diy-dream/shower-water-reusable/workspace/stm32-shower-water-reusable-stm32l412kb/Core/Src/stripEffects.c

/*
 * stripEffects.c
 *
 *  Created on: Aug 22, 2020
 *      Author: Alan
 */

#include "stripEffects.h"
#include "WS2812.h"

extern void setLEDcolor(uint32_t LEDnumber, uint8_t RED, uint8_t GREEN,
		uint8_t BLUE);

/* this array holds the RGB values to represent
 * a color wheel using 256 steps on each emitter
 * 256^3 = 16777216 colors
 * It was taken from http://eliaselectronics.com/
 */
uint8_t colorsFull[766][3] = { { 255, 0, 0 }, { 254, 1, 0 }, { 253, 2, 0 }, {
		252, 3, 0 }, { 251, 4, 0 }, { 250, 5, 0 }, { 249, 6, 0 }, { 248, 7, 0 },
		{ 247, 8, 0 }, { 246, 9, 0 }, { 245, 10, 0 }, { 244, 11, 0 }, { 243, 12,
				0 }, { 242, 13, 0 }, { 241, 14, 0 }, { 240, 15, 0 }, { 239, 16,
				0 }, { 238, 17, 0 }, { 237, 18, 0 }, { 236, 19, 0 }, { 235, 20,
				0 }, { 234, 21, 0 }, { 233, 22, 0 }, { 232, 23, 0 }, { 231, 24,
				0 }, { 230, 25, 0 }, { 229, 26, 0 }, { 228, 27, 0 }, { 227, 28,
				0 }, { 226, 29, 0 }, { 225, 30, 0 }, { 224, 31, 0 }, { 223, 32,
				0 }, { 222, 33, 0 }, { 221, 34, 0 }, { 220, 35, 0 }, { 219, 36,
				0 }, { 218, 37, 0 }, { 217, 38, 0 }, { 216, 39, 0 }, { 215, 40,
				0 }, { 214, 41, 0 }, { 213, 42, 0 }, { 212, 43, 0 }, { 211, 44,
				0 }, { 210, 45, 0 }, { 209, 46, 0 }, { 208, 47, 0 }, { 207, 48,
				0 }, { 206, 49, 0 }, { 205, 50, 0 }, { 204, 51, 0 }, { 203, 52,
				0 }, { 202, 53, 0 }, { 201, 54, 0 }, { 200, 55, 0 }, { 199, 56,
				0 }, { 198, 57, 0 }, { 197, 58, 0 }, { 196, 59, 0 }, { 195, 60,
				0 }, { 194, 61, 0 }, { 193, 62, 0 }, { 192, 63, 0 }, { 191, 64,
				0 }, { 190, 65, 0 }, { 189, 66, 0 }, { 188, 67, 0 }, { 187, 68,
				0 }, { 186, 69, 0 }, { 185, 70, 0 }, { 184, 71, 0 }, { 183, 72,
				0 }, { 182, 73, 0 }, { 181, 74, 0 }, { 180, 75, 0 }, { 179, 76,
				0 }, { 178, 77, 0 }, { 177, 78, 0 }, { 176, 79, 0 }, { 175, 80,
				0 }, { 174, 81, 0 }, { 173, 82, 0 }, { 172, 83, 0 }, { 171, 84,
				0 }, { 170, 85, 0 }, { 169, 86, 0 }, { 168, 87, 0 }, { 167, 88,
				0 }, { 166, 89, 0 }, { 165, 90, 0 }, { 164, 91, 0 }, { 163, 92,
				0 }, { 162, 93, 0 }, { 161, 94, 0 }, { 160, 95, 0 }, { 159, 96,
				0 }, { 158, 97, 0 }, { 157, 98, 0 }, { 156, 99, 0 }, { 155, 100,
				0 }, { 154, 101, 0 }, { 153, 102, 0 }, { 152, 103, 0 }, { 151,
				104, 0 }, { 150, 105, 0 }, { 149, 106, 0 }, { 148, 107, 0 }, {
				147, 108, 0 }, { 146, 109, 0 }, { 145, 110, 0 },
		{ 144, 111, 0 }, { 143, 112, 0 }, { 142, 113, 0 }, { 141, 114, 0 }, {
				140, 115, 0 }, { 139, 116, 0 }, { 138, 117, 0 },
		{ 137, 118, 0 }, { 136, 119, 0 }, { 135, 120, 0 }, { 134, 121, 0 }, {
				133, 122, 0 }, { 132, 123, 0 }, { 131, 124, 0 },
		{ 130, 125, 0 }, { 129, 126, 0 }, { 128, 127, 0 }, { 127, 128, 0 }, {
				126, 129, 0 }, { 125, 130, 0 }, { 124, 131, 0 },
		{ 123, 132, 0 }, { 122, 133, 0 }, { 121, 134, 0 }, { 120, 135, 0 }, {
				119, 136, 0 }, { 118, 137, 0 }, { 117, 138, 0 },
		{ 116, 139, 0 }, { 115, 140, 0 }, { 114, 141, 0 }, { 113, 142, 0 }, {
				112, 143, 0 }, { 111, 144, 0 }, { 110, 145, 0 },
		{ 109, 146, 0 }, { 108, 147, 0 }, { 107, 148, 0 }, { 106, 149, 0 }, {
				105, 150, 0 }, { 104, 151, 0 }, { 103, 152, 0 },
		{ 102, 153, 0 }, { 101, 154, 0 }, { 100, 155, 0 }, { 99, 156, 0 }, { 98,
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

void stripEffect_AllColors(uint32_t interval) {
	uint32_t index = 0;
	uint32_t led;

	while (1) {
		for (led = 0; led < LED_NUMBER; led++)
			setLEDcolor(led, colorsFull[index + led][0],
					colorsFull[index + led][1], colorsFull[index + led][2]);

		index++;

		if ((index + led) >= 766)
			index = 0;

		osDelay(interval);
	}
}

void stripEffect_ColorWheel(uint32_t interval) {
	uint32_t index = 0;
	uint32_t led, colorIndex;

	while (1) {
		for (led = 0; led < LED_NUMBER; led++) {
			colorIndex = (index + led * (766 / LED_NUMBER)) % 766;
			setLEDcolor(led, colorsFull[colorIndex][0],
					colorsFull[colorIndex][1], colorsFull[colorIndex][2]);
		}
		index += (766 / LED_NUMBER);
		index %= 766;
		osDelay(interval);
	}
}

void stripEffect_CircularRing(uint32_t interval, uint8_t red, uint8_t green,
		uint8_t blue) {
	uint32_t index = 0;

	while (1) {
		setWHOLEcolor(0x00, 0x00, 0x00);
		setLEDcolor(index, red, green, blue);
		index++;

		if (index >= LED_NUMBER)
			index = 0;

		osDelay(interval);
	}
}

// the interval should be in the 300-1000 range for best visual effect
void stripEffect_HeartBeat(uint32_t interval, uint8_t red, uint8_t green,
		uint8_t blue) {
	uint8_t redInc, greenInc, blueInc;
	uint8_t maxRed, maxGreen, maxBlue;

	redInc = red / HEARTBEAT_STEPS;
	greenInc = green / HEARTBEAT_STEPS;
	blueInc = blue / HEARTBEAT_STEPS;

	maxRed = redInc * (HEARTBEAT_STEPS - 1);
	maxGreen = greenInc * (HEARTBEAT_STEPS - 1);
	maxBlue = blueInc * (HEARTBEAT_STEPS - 1);

	uint32_t index;

	setWHOLEcolor(0, 0, 0);

	while (1) {
		// first stroke
		for (index = 0; index < HEARTBEAT_STEPS; index++) {
			setWHOLEcolor(index * redInc, index * greenInc, index * blueInc);
			osDelay(interval / 50);
		}
		for (index = 0; index < HEARTBEAT_STEPS; index++) {
			setWHOLEcolor(maxRed - index * redInc, maxGreen - index * greenInc,
					maxBlue - index * blueInc);
			osDelay(interval / 45);
		}
		// second stroke
		for (index = 0; index < HEARTBEAT_STEPS; index++) {
			setWHOLEcolor(index * redInc, index * greenInc, index * blueInc);
			osDelay(interval / 40);
		}
		for (index = 0; index < HEARTBEAT_STEPS; index++) {
			setWHOLEcolor(maxRed - index * redInc, maxGreen - index * greenInc,
					maxBlue - index * blueInc);
			osDelay(interval / 35);
		}
		// relax..
		osDelay(interval);
	}
}

void stripEffect_PatternMove(uint32_t interval, uint32_t parts, uint8_t red,
		uint8_t green, uint8_t blue) {
	uint32_t index = 0;
	uint32_t indexStep;
	uint32_t i;

	indexStep = LED_NUMBER / parts;

	setWHOLEcolor(0, 0, 0);

	while (1) {
		setWHOLEcolor(0, 0, 0);
		for (i = 0; i < parts; i++)
			setLEDcolor(index + i * indexStep, red, green, blue);
		index++;

		if (index >= LED_NUMBER)
			index = 0;

		osDelay(interval);
	}
}

void stripEffect_FullEmpty(uint32_t interval, uint8_t red, uint8_t green,
		uint8_t blue) {
	uint32_t index = 0;

	setWHOLEcolor(0, 0, 0);

	while (1) {
		for (index = 0; index < LED_NUMBER; index++) {
			setLEDcolor(index, red, green, blue);
			osDelay(interval);
		}

		for (index = 0; index < LED_NUMBER; index++) {
			setLEDcolor(index, 0, 0, 0);
			osDelay(interval);
		}
	}
}

void stripEffect_FromTo(uint32_t interval, uint32_t steps, uint8_t redA,
		uint8_t greenA, uint8_t blueA, uint8_t redB, uint8_t greenB,
		uint8_t blueB) {
	uint32_t i;
	int16_t deltaRed, deltaGreen, deltaBlue;

	deltaRed = ((int32_t) redB - (int32_t) redA) / (int32_t) steps;
	deltaGreen = ((int32_t) greenB - (int32_t) greenA) / (int32_t) steps;
	deltaBlue = ((int32_t) blueB - (int32_t) blueA) / (int32_t) steps;

	for (i = 0; i < steps; i++) {
		setWHOLEcolor(redA + i * deltaRed, greenA + i * deltaGreen,
				+blueA + i * deltaBlue);
		osDelay(interval / steps);
	}
}

void stripEffect_AlternateColors(uint32_t interval, uint32_t steps,
		uint8_t redA, uint8_t greenA, uint8_t blueA, uint8_t redB,
		uint8_t greenB, uint8_t blueB) {
	uint32_t i;
	int32_t deltaRed, deltaGreen, deltaBlue;

	deltaRed = ((int32_t) redB - (int32_t) redA) / (int32_t) steps;
	deltaGreen = ((int32_t) greenB - (int32_t) greenA) / (int32_t) steps;
	deltaBlue = ((int32_t) blueB - (int32_t) blueA) / (int32_t) steps;

	while (1) {
		for (i = 0; i < steps; i++) {
			setWHOLEcolor(redA + i * deltaRed, greenA + i * deltaGreen,
					+blueA + i * deltaBlue);
			osDelay(interval / steps);
		}
		for (i = steps - 1; i > 0; i--) {
			setWHOLEcolor(redA + i * deltaRed, greenA + i * deltaGreen,
					+blueA + i * deltaBlue);
			osDelay(interval / steps);
		}
	}
}
